hidetatz/yomogame/src/nes/osd.cpp

#include <Arduino.h>
#include <SPI.h>
#include <SD.h>
#include <FS.h>
#include "hw_config.h"
#include "nes_bridge.h"

#if ENABLE_SOUND
#include <driver/i2s.h>
#endif

#include <string.h>
#include <stdarg.h>

extern "C" {
#include "noftypes.h"
#include "bitmap.h"
#include "osd.h"
#include "nofrendo.h"
#include "nesinput.h"
#include "event.h"
#include "nofconfig.h"
}

#define NES_SCREEN_WIDTH 256
#define NES_SCREEN_HEIGHT 240

// Full, uncropped NES frame; FramePusher (see nes_scene.h) scales this down
// to fit the 240-wide panel, letterboxed top/bottom, instead of this file
// centre-cropping the sides off.
#define OUT_WIDTH  NES_SCREEN_WIDTH
#define OUT_HEIGHT NES_SCREEN_HEIGHT
#define CROP_X ((NES_SCREEN_WIDTH - OUT_WIDTH) / 2)

#define DISPLAY_WIDTH OUT_WIDTH
#define DISPLAY_HEIGHT OUT_HEIGHT

#ifndef AUDIO_SAMPLE_RATE
#define AUDIO_SAMPLE_RATE 22050
#endif
#define AUDIO_GAIN 100
#define TARGET_FRAME_MICROS 16666

int master_volume = 100;
bool show_fps = false;
bool select_pressed = false;
static bool runtime_sound_enabled = false;

static inline uint16_t rgb_to_565(uint8_t r, uint8_t g, uint8_t b) {
  return (uint16_t)(((r & 0xF8) << 8) | ((g & 0xFC) << 3) | (b >> 3));
}

static void show_magic() {}   // DSN intro splash removed (dropped turning.h)

static int16_t mono_buffer[2048];
static void (*emulator_audio_callback)(void *buffer, int length) = NULL;
 
static uint16_t myPalette565[256];
static uint16_t myPalette565_swapped[256];
static bitmap_t *game_bitmap = NULL;
static bool video_ready = false;
static uint16_t *frame_buffer = NULL;  
static bool low_mem_video_mode = false;
 
unsigned long frame_start_time = 0;
unsigned long frame_count = 0;
unsigned long last_fps_update = 0;
int current_fps = 0;
 
#define INP_JOYPAD0 0x0001
static nesinput_t joypad_p1;

#define HW_MASK_A 0x01
#define HW_MASK_B 0x02
#define HW_MASK_SELECT 0x04
#define HW_MASK_START 0x08
#define HW_MASK_UP 0x10
#define HW_MASK_DOWN 0x20
#define HW_MASK_LEFT 0x40
#define HW_MASK_RIGHT 0x80

#define INP_PAD_A 0x01
#define INP_PAD_B 0x02
#define INP_PAD_SELECT 0x04
#define INP_PAD_START 0x08
#define INP_PAD_UP 0x10
#define INP_PAD_DOWN 0x20
#define INP_PAD_LEFT 0x40
#define INP_PAD_RIGHT 0x80
 
esp_timer_handle_t nes_timer_handle = NULL;
void (*emu_timer_callback)(void) = NULL;

void IRAM_ATTR timer_callback_handler(void *arg) {
  if (emu_timer_callback) emu_timer_callback();
}
 
extern char *global_rom_data;
extern int global_rom_size;

extern "C" bool vid_preload_rom(const char *path);
extern "C" int osd_rom_open(const char *path);
extern "C" int osd_rom_read(void *dst, int len);
extern "C" void osd_rom_close(void);
 
// The DSN on-device ROM picker + preloader is replaced by NesScene (yomogame
// scans the SD itself and hands the path to nofrendo_main; ROM bytes stream in
// through osd_rom_open/read/close). Kept out of the build:
#if 0
#define MAX_GAMES 50
struct {
  char names[MAX_GAMES][32];
  int count;
  int selected;
} game_list = {{}, 0, 0};

int menu_volume = 100;
bool menu_brightness = true;

void scan_games() {
  File root = SD.open("/");
  game_list.count = 0;
  
  while (true) {
    File entry = root.openNextFile();
    if (!entry) break;
    
    if (!entry.isDirectory() && game_list.count < MAX_GAMES) {
      String name = entry.name();
      if (name.endsWith(".nes") || name.endsWith(".NES")) {
        strncpy(game_list.names[game_list.count], entry.name(), 31);
        game_list.names[game_list.count][31] = '\0';
        game_list.count++;
      }
    }
    entry.close();
  }
  root.close();
}
 
void draw_menu() {
  tft.fillScreen(0x0000);  
  delay(100);
   
  tft.drawFilledRect(0, 0, DISPLAY_WIDTH, 50, 0xF800);  
  delay(50);
   
  Serial.println("[MENU] Drawing title...");
  tft.drawString(20, 10, "NES EMULATOR", 0xFFFF, 0xF800, 2);
   
  Serial.println("[MENU] Drawing game list...");
  int start_y = 70;
  for (int i = 0; i < game_list.count && i < 4; i++) {
    uint16_t color = (i == game_list.selected) ? 0xF800 : 0xFFFF;  
    char display_name[32];
    strncpy(display_name, game_list.names[i], 31);
    display_name[31] = '\0';
     
    char *dot = strchr(display_name, '.');
    if (dot) *dot = '\0';
    
    Serial.printf("  [%d] %s\n", i, display_name);
    tft.drawString(20, start_y + (i * 30), display_name, color, 0x0000, 1);
  }
  
  Serial.println("[MENU] Drawing controls...");
  tft.drawString(10, 220, "UP/DOWN:Select  A:Play  SELECT:Settings", 0xFFFF, 0x0000, 1);
  delay(100);
}

void draw_settings() {
  tft.fillScreen(0x0000);
  delay(50);
   
  tft.drawFilledRect(0, 0, DISPLAY_WIDTH, 50, 0x001F); 
  
  tft.drawString(20, 10, "SETTINGS", 0xFFFF, 0x001F, 2);
  
  tft.drawString(20, 80, "Volume: ", 0xFFFF, 0x0000, 1);
  char vol_str[10];
  snprintf(vol_str, 10, "%d%%", menu_volume);
  tft.drawString(100, 80, vol_str, 0x07E0, 0x0000, 1);
  
  tft.drawString(10, 220, "UP/DOWN:Volume  A:Save  B:Back", 0xFFFF, 0x0000, 1);
}

extern "C" int show_menu() {
  Serial.println("\n[MENU] Starting menu system...");

  show_magic();
  
  scan_games();
  Serial.printf("[MENU] Found %d games\n", game_list.count);
  
  if (game_list.count == 0) {
    Serial.println("[MENU] No games found!");
    tft.fillScreen(0xF800); 
    delay(3000);
    return -1;
  }
  
  game_list.selected = 0;
  int top_index = 0; 
  bool in_menu = true;
  unsigned long last_input = 0;
  int last_selected = -1;
  
  bool needs_full_redraw = true;
  bool needs_list_redraw = false;

  auto draw_menu_item = [&](int screen_idx, int game_idx, bool selected) {
    int y_pos = 50 + (screen_idx * 40);
    uint16_t bg = selected ? 0xF800 : 0x0000;
    uint16_t fg = 0xFFFF;
    
    char display_name[32];
    strncpy(display_name, game_list.names[game_idx], 31);
    display_name[31] = '\0';
    char *dot = strchr(display_name, '.');
    if (dot) *dot = '\0';

    tft.drawFilledRect(0, y_pos - 5, DISPLAY_WIDTH, 35, bg);
    tft.drawString(20, y_pos, display_name, fg, bg, 1);
  };
  
  while (in_menu) {
    if (needs_full_redraw) {
      tft.fillScreen(0x0000); 
      tft.drawString(10, 10, "GAME MENU", 0xFFFF, 0x0000, 2);
      
      for (int i = 0; i < 4 && (top_index + i) < game_list.count; i++) {
        draw_menu_item(i, top_index + i, (top_index + i) == game_list.selected);
      }
      
      tft.drawString(10, DISPLAY_HEIGHT - 40, "UP/DN: Select", 0x07E0, 0x0000, 1);
      tft.drawString(10, DISPLAY_HEIGHT - 20, "A: Play  SEL: Settings", 0x07E0, 0x0000, 1);
      
      last_selected = game_list.selected;
      needs_full_redraw = false;
      needs_list_redraw = false;
    } 
    else if (needs_list_redraw) {
      tft.drawFilledRect(0, 45, DISPLAY_WIDTH, 155, 0x0000); 
      
      for (int i = 0; i < 4 && (top_index + i) < game_list.count; i++) {
        draw_menu_item(i, top_index + i, (top_index + i) == game_list.selected);
      }
      
      last_selected = game_list.selected;
      needs_list_redraw = false;
    } 
    else if (last_selected != game_list.selected) {
      if (last_selected >= top_index && last_selected < top_index + 4) {
        draw_menu_item(last_selected - top_index, last_selected, false);
      }
      draw_menu_item(game_list.selected - top_index, game_list.selected, true);
      last_selected = game_list.selected;
    }
    
    int hw = nes_get_gamepad_state();
    
    if ((millis() - last_input) > 150) {
      if (hw & HW_MASK_UP) {
        if (game_list.selected > 0) {
          game_list.selected--;
          if (game_list.selected < top_index) {
            top_index = game_list.selected;
            needs_list_redraw = true; 
          }
          last_input = millis();
        }
      }
      if (hw & HW_MASK_DOWN) {
        if (game_list.selected < game_list.count - 1) {
          game_list.selected++;
          if (game_list.selected >= top_index + 4) {
            top_index = game_list.selected - 3;
            needs_list_redraw = true;
          }
          last_input = millis();
        }
      }
      if (hw & HW_MASK_A) {
        tft.fillScreen(0x0000);  
        delay(300);
        return game_list.selected;
      }
      if (hw & HW_MASK_SELECT) {
        bool in_settings = true;
        unsigned long settings_input = 0;
        int last_menu_volume = -1;
        bool settings_full_redraw = true;
        
        while (in_settings) {
          if (settings_full_redraw) {
            tft.fillScreen(0x0000);
            tft.drawString(10, 10, "VOLUME SETTINGS", 0xFFFF, 0x0000, 2);
            tft.drawString(10, DISPLAY_HEIGHT - 40, "UP/DN: Adjust", 0x07E0, 0x0000, 1);
            tft.drawString(10, DISPLAY_HEIGHT - 20, "A: Save  B: Cancel", 0x07E0, 0x0000, 1);
            settings_full_redraw = false;
            last_menu_volume = -1;
          }

          if (last_menu_volume != menu_volume) {
            char vol_str[20];
            sprintf(vol_str, "Vol: %d%%", menu_volume);
            tft.drawFilledRect(20, 60, 200, 20, 0x0000);
            tft.drawString(20, 60, vol_str, 0x07E0, 0x0000, 2);

            int bar_width = (menu_volume * (DISPLAY_WIDTH - 40)) / 200;
            tft.drawFilledRect(20, 120, DISPLAY_WIDTH - 40, 30, 0x4208); 
            tft.drawFilledRect(20, 120, bar_width, 30, 0xF800);

            last_menu_volume = menu_volume;
          }
          
          int hw2 = nes_get_gamepad_state();
          
          if ((millis() - settings_input) > 150) {
            if (hw2 & HW_MASK_UP) {
              menu_volume = min(200, menu_volume + 10);
              master_volume = menu_volume;
              settings_input = millis();
            }
            if (hw2 & HW_MASK_DOWN) {
              menu_volume = max(0, menu_volume - 10);
              master_volume = menu_volume;
              settings_input = millis();
            }
            if (hw2 & HW_MASK_A || hw2 & HW_MASK_B) {
              in_settings = false;
            }
          }
          delay(50);
        }
        last_input = millis();
        needs_full_redraw = true; 
      }
    }
    delay(20);
  }
  return -1;
}

extern "C" const char *get_selected_game() {
  static char game_path[64];
  if (game_list.selected < game_list.count) {
    snprintf(game_path, 64, "/%s", game_list.names[game_list.selected]);
    return game_path;
  }
  return "/mario.nes";  // Default fallback
}

extern "C" char *osd_getromdata(void) {
  const char *rom_path = get_selected_game();
  
  Serial.printf("[ROM] osd_getromdata loading: %s\n", rom_path);
  Serial.flush();
  
  if (global_rom_data == NULL) {
    Serial.println("[ROM] global_rom_data is NULL - loading from SD...");
    Serial.flush();
    
    bool loaded = false;
    try {
      loaded = vid_preload_rom(rom_path);
    } catch (...) {
      Serial.println("[ROM] EXCEPTION during ROM preload!");
      loaded = false;
    }
    
    if (!loaded) {
      Serial.printf("[ROM] CRITICAL: Failed to load ROM file: %s\n", rom_path);
      return NULL;
    }
  }
  
  if (global_rom_data == NULL) {
    Serial.println("[ROM] FATAL: Still no ROM data after load attempt!");
    return NULL;
  }

  Serial.printf("[ROM] ROM ready: %d bytes\n", global_rom_size);
  return global_rom_data;
}

extern "C" void osd_release_romdata(void) {
  if (global_rom_data) {
    free(global_rom_data);
    global_rom_data = NULL;
    global_rom_size = 0;
  }
}
#endif  // DSN ROM picker / preloader

extern "C" int osd_init_sound(void) {
  if (!runtime_sound_enabled) {
    Serial.println("Audio disabled by runtime config (-sound not set)");
    return 0;
  }
#if ENABLE_SOUND
  Serial.println("Initializing I2S audio...");
  i2s_config_t i2s_config = {
    .mode = (i2s_mode_t)(I2S_MODE_MASTER | I2S_MODE_TX),
    .sample_rate = AUDIO_SAMPLE_RATE,
    .bits_per_sample = I2S_BITS_PER_SAMPLE_16BIT,
    .channel_format = I2S_CHANNEL_FMT_RIGHT_LEFT,
    .communication_format = I2S_COMM_FORMAT_I2S_MSB,
    .intr_alloc_flags = ESP_INTR_FLAG_LEVEL1,
    .dma_buf_count = 8,
    .dma_buf_len = 512,
    .use_apll = true,
    .tx_desc_auto_clear = true
  };
  i2s_pin_config_t pin_config = {
    .bck_io_num = I2S_BCK,
    .ws_io_num = I2S_WS,
    .data_out_num = I2S_DO,
    .data_in_num = I2S_PIN_NO_CHANGE
  };

  esp_err_t err;
  if ((err = i2s_driver_install(I2S_NUM_0, &i2s_config, 0, NULL)) != ESP_OK) {
    Serial.printf("I2S driver install failed: %d\n", err);
    return -1;
  }
  if ((err = i2s_set_pin(I2S_NUM_0, &pin_config)) != ESP_OK) {
    Serial.printf("I2S set pin failed: %d\n", err);
    return -1;
  }
  i2s_set_clk(I2S_NUM_0, AUDIO_SAMPLE_RATE, I2S_BITS_PER_SAMPLE_16BIT, I2S_CHANNEL_STEREO);
  Serial.println("I2S audio initialized successfully");
  return 0;
#else
  Serial.println("Sound disabled in configuration");
  return 0;
#endif
}

extern "C" void osd_getsoundinfo(sndinfo_t *info) {
  info->sample_rate = AUDIO_SAMPLE_RATE;
  info->bps = 16;
}

extern "C" void osd_setsound(void (*playfunc)(void *buffer, int length)) {
  emulator_audio_callback = runtime_sound_enabled ? playfunc : NULL;
}

extern "C" void osd_stopsound(void) {
  if (!runtime_sound_enabled) return;
#if ENABLE_SOUND
  i2s_zero_dma_buffer(I2S_NUM_0);
#endif
}

extern "C" void osd_writesound(void *stream, int len) {}

extern "C" void osd_initvideo(int *lines) {
  *lines = NES_SCREEN_HEIGHT;
  Serial.printf("osd_initvideo called, lines=%d\n", *lines);
}

extern "C" void osd_shutdownvideo() {}

extern "C" void osd_setscreen(int x, int y, int width, int height) {}

extern "C" void osd_setpalette(rgb_t *pal) {
  if (!pal) return;
  for (int i = 0; i < 256; i++) {
    uint16_t c = rgb_to_565(pal[i].r, pal[i].g, pal[i].b);
    myPalette565[i] = c;
    myPalette565_swapped[i] = __builtin_bswap16(c);
  }
}

extern "C" int nes_get_gamepad_state();

extern "C" void osd_getinput(void) {
  int hw = nes_get_gamepad_state();
  int nes_data = 0;

  if (hw & HW_MASK_A) nes_data |= INP_PAD_A;
  if (hw & HW_MASK_B) nes_data |= INP_PAD_B;
  if (hw & HW_MASK_SELECT) nes_data |= INP_PAD_SELECT;
  if (hw & HW_MASK_START) nes_data |= INP_PAD_START;
  if (hw & HW_MASK_UP) nes_data |= INP_PAD_UP;
  if (hw & HW_MASK_DOWN) nes_data |= INP_PAD_DOWN;
  if (hw & HW_MASK_LEFT) nes_data |= INP_PAD_LEFT;
  if (hw & HW_MASK_RIGHT) nes_data |= INP_PAD_RIGHT;
  joypad_p1.data = nes_data;
}

extern "C" int osd_init() {
  Serial.println("[OSD] Initializing...");
  Serial.printf("[OSD] Heap=%u, SPIRAM=%u\n", esp_get_free_heap_size(), heap_caps_get_free_size(MALLOC_CAP_SPIRAM));
  
  Serial.println("[OSD] Initializing joypad...");
  joypad_p1.type = INP_JOYPAD0;
  joypad_p1.data = 0;
  
  input_register(&joypad_p1);
  Serial.println("[OSD] Input registered successfully");
  
  if (osd_init_sound() != 0) { 
    Serial.println("[OSD] Sound Init FAILED"); 
  }
  
  Serial.printf("[OSD] Post-init Heap=%u, SPIRAM=%u\n", esp_get_free_heap_size(), heap_caps_get_free_size(MALLOC_CAP_SPIRAM));
  Serial.println("[OSD] Initialization complete");
  return 0;
}

extern "C" void osd_shutdown() {
  if (nes_timer_handle) {
    esp_timer_stop(nes_timer_handle);
    esp_timer_delete(nes_timer_handle);
  }
}

extern "C" int osd_installtimer(int freq, void *func, int func_param, void *func2, int func2_param) {
  emu_timer_callback = (void (*)(void))func;
  const esp_timer_create_args_t timer_args = { .callback = &timer_callback_handler, .name = "nes_timer" };
  esp_timer_create(&timer_args, &nes_timer_handle);
  esp_timer_start_periodic(nes_timer_handle, 1000000 / freq);
  return 0;
}

extern "C" int osd_gettime(void) {
  return millis();
}

extern "C" int osd_makesnapname(char *buf, int len) {
  return 0;
}

extern "C" void osd_getmouse(int *x, int *y, int *button) {
  *x = 0;
  *y = 0;
  *button = 0;
}

char *global_rom_data = NULL;
int global_rom_size = 0;
static File rom_stream_file;

#if 0  // unused: ROM streams via osd_rom_open/read/close
extern "C" bool vid_preload_rom(const char *path) {
  if (global_rom_data) {
    free(global_rom_data);
    global_rom_data = NULL;
  }
  
  Serial.printf("[ROM] Opening file: %s\n", path);
  Serial.flush();
  delay(100);
  
  File file;
  try {
    file = SD.open(path, FILE_READ);
  } catch (...) {
    Serial.println("[ROM] EXCEPTION during SD.open()!");
    return false;
  }
  
  if (!file) {
    Serial.println("[ROM] Failed to open file");
    return false;
  }
  
  global_rom_size = file.size();
  Serial.printf("[ROM] File size: %d bytes\n", global_rom_size);
  
  Serial.println("[ROM] Allocating memory...");
  global_rom_data = (char *)heap_caps_malloc(global_rom_size, MALLOC_CAP_SPIRAM | MALLOC_CAP_8BIT);
  if (!global_rom_data) {
    Serial.println("[ROM] SPIRAM allocation failed, trying regular heap...");
    global_rom_data = (char *)malloc(global_rom_size);
  }
  
  if (!global_rom_data) {
    Serial.println("[ROM] Memory allocation failed!");
    file.close();
    return false;
  }
  
  Serial.println("[ROM] Reading file into memory...");
  size_t bytes_read = file.readBytes(global_rom_data, global_rom_size);
  file.close();
  
  Serial.printf("[ROM] Read %d bytes\n", bytes_read);
  if (bytes_read != global_rom_size) {
    Serial.printf("[ROM] Error: Expected %d bytes, got %d\n", global_rom_size, bytes_read);
    free(global_rom_data);
    global_rom_data = NULL;
    return false;
  }
  
  Serial.println("[ROM] ROM loaded successfully!");
  return true;
}
#endif  // vid_preload_rom

extern "C" void IRAM_ATTR osd_blit(bitmap_t *bmp) {
  if (!video_ready || !bmp || !bmp->line || !bmp->line[0] || !frame_buffer) {
    return;
  }

  // Centre-crop the 256-wide NES frame to the 240-wide panel. Pre-swapped
  // (big-endian) RGB565 so nes_blit_frame() can DMA it with no swap step.
  for (int y = 0; y < NES_SCREEN_HEIGHT; y++) {
    uint8_t *src = bmp->line[y] + CROP_X;
    uint16_t *dst = &frame_buffer[y * OUT_WIDTH];
    for (int x = 0; x < OUT_WIDTH; x++) {
      dst[x] = myPalette565_swapped[src[x]];
    }
  }
}

extern "C" void vid_flush() {
  static unsigned long last_display_update = 0;
  static bool tried_frame_buffer_alloc = false;

  frame_start_time = micros();
  (void)tried_frame_buffer_alloc;

  // The render target is owned by NesScene (double-buffered).
  frame_buffer = nes_framebuffer();

  if (frame_buffer) {
    osd_blit(game_bitmap);
  }

  unsigned long now = micros();
  if (frame_buffer && now - last_display_update > 16666) {
    unsigned long t1 = micros();
    nes_blit_frame(frame_buffer);
    unsigned long push_t = micros() - t1;
    last_display_update = now;

    static unsigned long last_print = 0;
    if (millis() - last_print > 3000) {
      Serial.printf("push=%luus emul_fps=%d\n", push_t, current_fps);
      last_print = millis();
    }
  }

  if (runtime_sound_enabled && emulator_audio_callback) {
    // Ask the APU for as many samples as real time has elapsed since the last
    // call, not a fixed 60fps quota. When the emulator runs below 60fps this
    // keeps average production at AUDIO_SAMPLE_RATE and stops the ring
    // underrunning (which is what caused the crackle).
    static unsigned long last_audio_us = 0;
    unsigned long t = micros();
    int samples_needed;
    if (last_audio_us == 0) {
      samples_needed = AUDIO_SAMPLE_RATE / 60;
    } else {
      samples_needed = (int)((uint64_t)(t - last_audio_us) * AUDIO_SAMPLE_RATE / 1000000ULL);
    }
    last_audio_us = t;
    if (samples_needed < 1) samples_needed = 1;
    if (samples_needed > 2048) samples_needed = 2048;   // mono_buffer cap

    emulator_audio_callback(mono_buffer, samples_needed);
    nes_audio_push(mono_buffer, samples_needed);   // -> audio::Audio via ring
  }

  frame_count++;
  if (millis() - last_fps_update >= 1000) {
    current_fps = frame_count;
    frame_count = 0;
    last_fps_update = millis();
  }

  nes_post_frame();

  // Yield core 1 to the shell / volume / IDLE tasks. Every other frame is
  // enough to keep them alive and gives the emulator a bit more budget.
  static int yield_ctr = 0;
  if (++yield_ctr & 1) vTaskDelay(1);
}

extern "C" int vid_init(int width, int height, viddriver_t *osd_driver) {
  if (!game_bitmap) game_bitmap = bmp_create(NES_SCREEN_WIDTH, NES_SCREEN_HEIGHT, 0); 
  frame_buffer = NULL;
  low_mem_video_mode = false;
  video_ready = (game_bitmap && game_bitmap->data);
  Serial.printf("vid_init heap snapshot: heap=%u spiram=%u\n", esp_get_free_heap_size(), heap_caps_get_free_size(MALLOC_CAP_SPIRAM));
  Serial.printf("vid_init: bitmap %p, frame_buffer %p, ready %d, deferred_fb_alloc=1\n", game_bitmap, frame_buffer, video_ready);
  return video_ready ? 0 : -1;
}

extern "C" int osd_rom_open(const char *path) {
  if (rom_stream_file) {
    rom_stream_file.close();
  }

  Serial.printf("[ROM] Streaming open: %s\n", path ? path : "(null)");
  rom_stream_file = SD.open(path, FILE_READ);
  if (!rom_stream_file) {
    Serial.println("[ROM] Streaming open failed");
    return -1;
  }
  return 0;
}

extern "C" int osd_rom_read(void *dst, int len) {
  if (!rom_stream_file || !dst || len <= 0) {
    return -1;
  }
  int n = rom_stream_file.read((uint8_t *)dst, len);
  return n;
}

extern "C" void osd_rom_close(void) {
  if (rom_stream_file) {
    rom_stream_file.close();
  }
}

extern "C" void vid_shutdown() {
  video_ready = false;
}

extern "C" int vid_setmode(int width, int height) {
  return 0;
}

extern "C" void vid_setpalette(rgb_t *pal) {
  osd_setpalette(pal);
}

extern "C" bitmap_t *vid_getbuffer() {
  if (!game_bitmap) game_bitmap = bmp_create(NES_SCREEN_WIDTH, NES_SCREEN_HEIGHT, 0);
  video_ready = (game_bitmap && game_bitmap->data);
  return game_bitmap;
}

extern "C" void osd_getvideoinfo(vidinfo_t *info) {
  info->default_width = NES_SCREEN_WIDTH;
  info->default_height = NES_SCREEN_HEIGHT;
  info->driver = 0;
}

extern "C" void osd_togglefullscreen(int code) {}

extern "C" char *osd_newextension(char *string, char *ext) {
  return string;
}

extern "C" void osd_fullname(char *fullname, const char *shortname) {
  strcpy(fullname, shortname);
}

extern "C" int osd_main(int argc, char *argv[]) {
  runtime_sound_enabled = false;
  for (int i = 1; i < argc; i++) {
    if (argv[i] && strcmp(argv[i], "-sound") == 0) {
      runtime_sound_enabled = true;
    }
    if (argv[i] && strcmp(argv[i], "-nosound") == 0) {
      runtime_sound_enabled = false;
    }
  }

  char *rom_name = "rom";
  if (argc > 0) rom_name = argv[argc - 1];
  return main_loop(rom_name, system_nes);
}

extern "C" int nofrendo_log_init(void) {
  return 0;
}

extern "C" void nofrendo_log_shutdown(void) {}

extern "C" int nofrendo_log_print(const char *s) {
  if (s) {
    Serial.print(s);
  }
  return 0;
}

extern "C" int nofrendo_log_printf(const char *format, ...) {
  char buf[256];
  va_list args;
  va_start(args, format);
  int written = vsnprintf(buf, sizeof(buf), format, args);
  va_end(args);
  Serial.print(buf);
  return written;
}

extern "C" void nofrendo_log_assert(int expr, int line, const char *file, char *msg) {
  if (!expr) {
    Serial.printf("ASSERT FAILED: %s:%d %s\n", file ? file : "?", line, msg ? msg : "");
  }
}
